FunDeckHermit/hw-communicator/firmware/wifi.py

from phew import server, connect_to_wifi

# helper method to put the pico into access point mode
def access_point(ssid, password = None):
  import network

  # start up network in access point mode  
  wlan = network.WLAN(network.AP_IF)
  wlan.config(essid=ssid)
  if password:
    wlan.config(password=password)
  else:    
    wlan.config(security=0) # disable password
  wlan.active(True)

  return wlan

@server.route("/random", methods=["GET"])
def random_number(request):
  min = int(request.query.get("min", 0))
  max = int(request.query.get("max", 100))
  return str(random.randint(min, max))

@server.catchall()
def catchall(request):
  return "Not found", 404


def connect():
    conn = connect_to_wifi("AIVD afluisterbug 632", "lisaenroy")
    print(conn)
    return False
